d3lta-v/SPEEEduino/Image Assets/Documentation/Board_Select.png

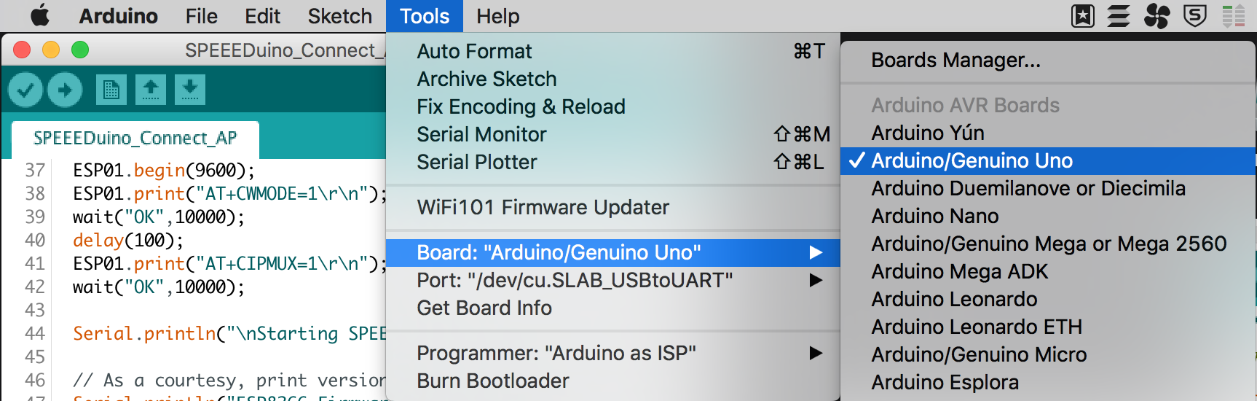
Image Assets/Documentation/Board_Select.png
