d3lta-v/SPEEEduino/Image Assets/Documentation/CP2102_Connected.jpg

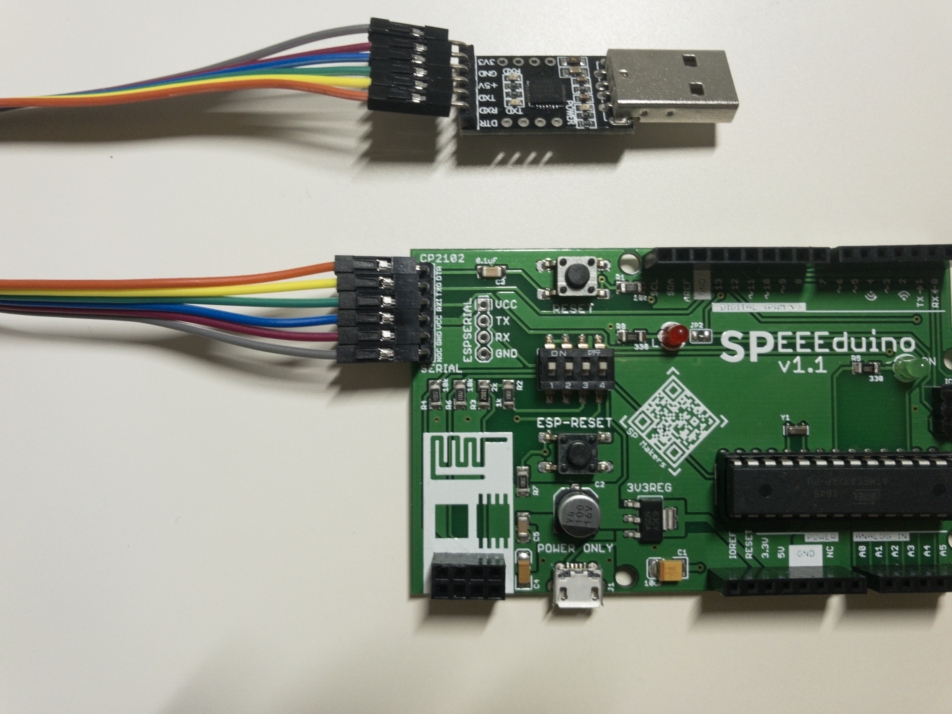
Image Assets/Documentation/CP2102_Connected.jpg
