d3lta-v/SPEEEduino/Image Assets/Documentation/Required_Tools.jpg

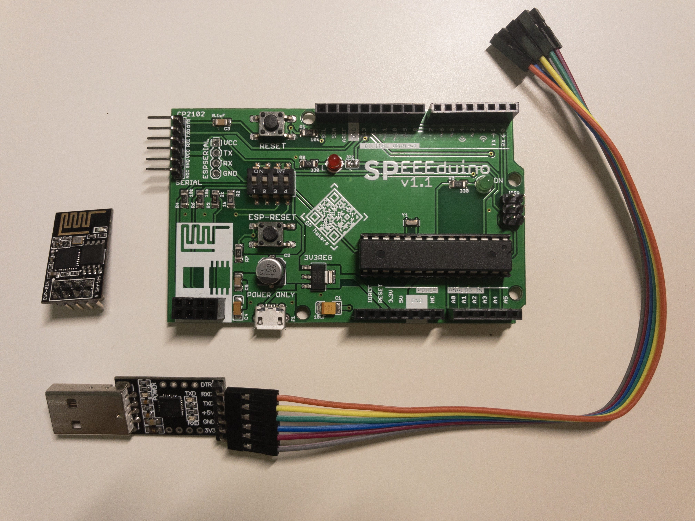
Image Assets/Documentation/Required_Tools.jpg
