d3lta-v/SPEEEduino/Image Assets/Documentation/Serial_Port_Select.png

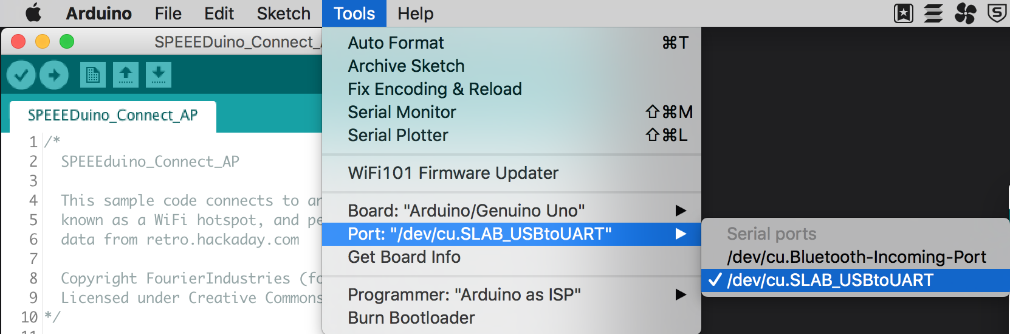
Image Assets/Documentation/Serial_Port_Select.png
